jpt1729/Alarm-Clock/photos/Screenshot 2025-06-30 102620.png

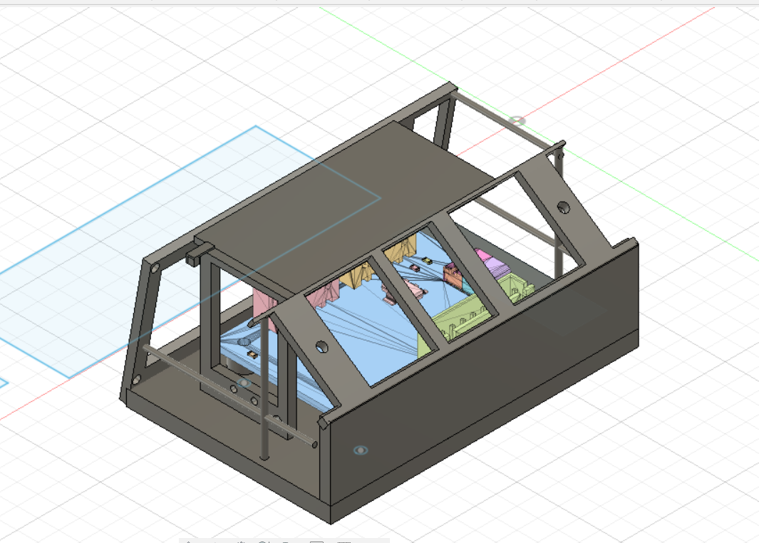
photos/Screenshot 2025-06-30 102620.png
