jpt1729/Alarm-Clock/photos/Screenshot 2025-07-01 180041.png

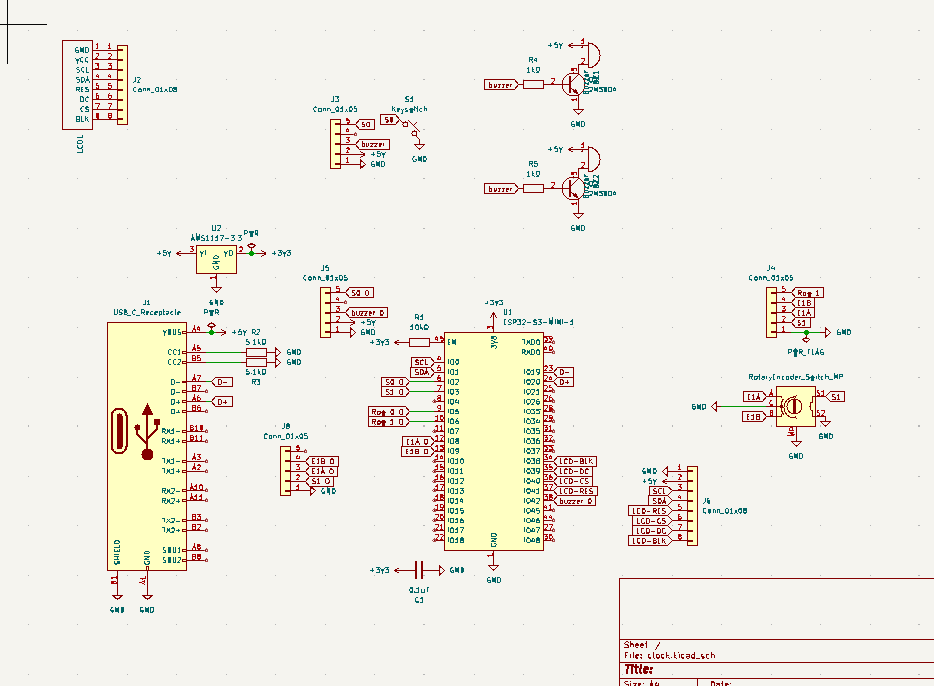
photos/Screenshot 2025-07-01 180041.png
