jpt1729/Alarm-Clock/photos/Screenshot 2025-07-02 110856.png

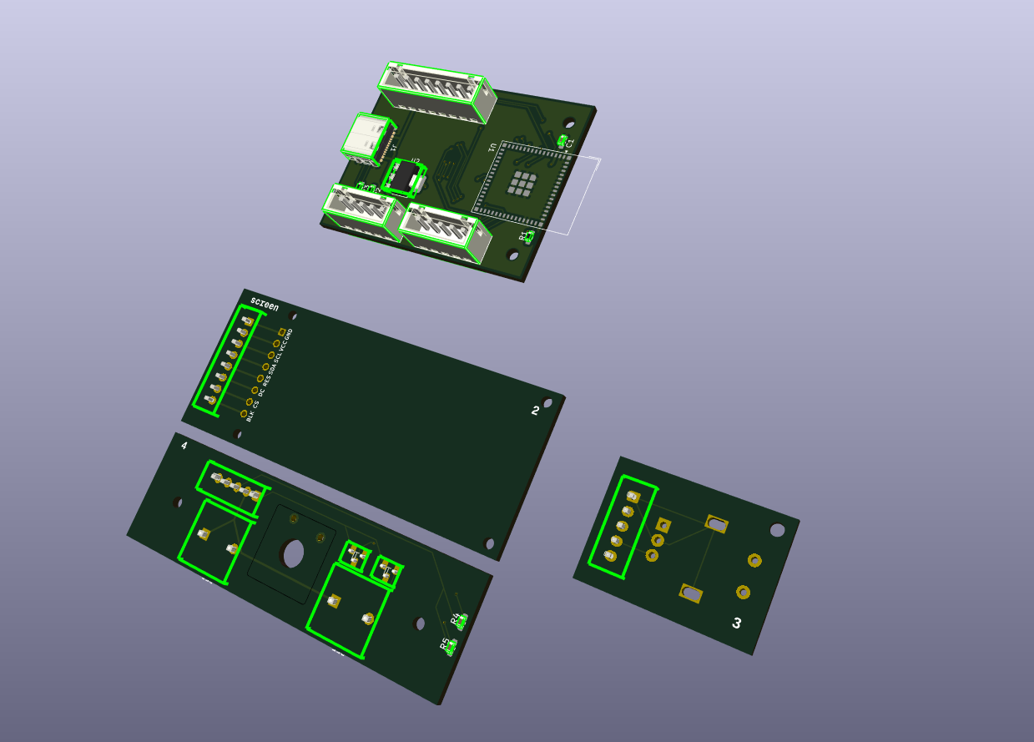
photos/Screenshot 2025-07-02 110856.png
